Kybernetika-SPSE/RP-Hovorka/rp_dokumentace/LateX zdrojový kód/pictures/IMG_0316.JPG

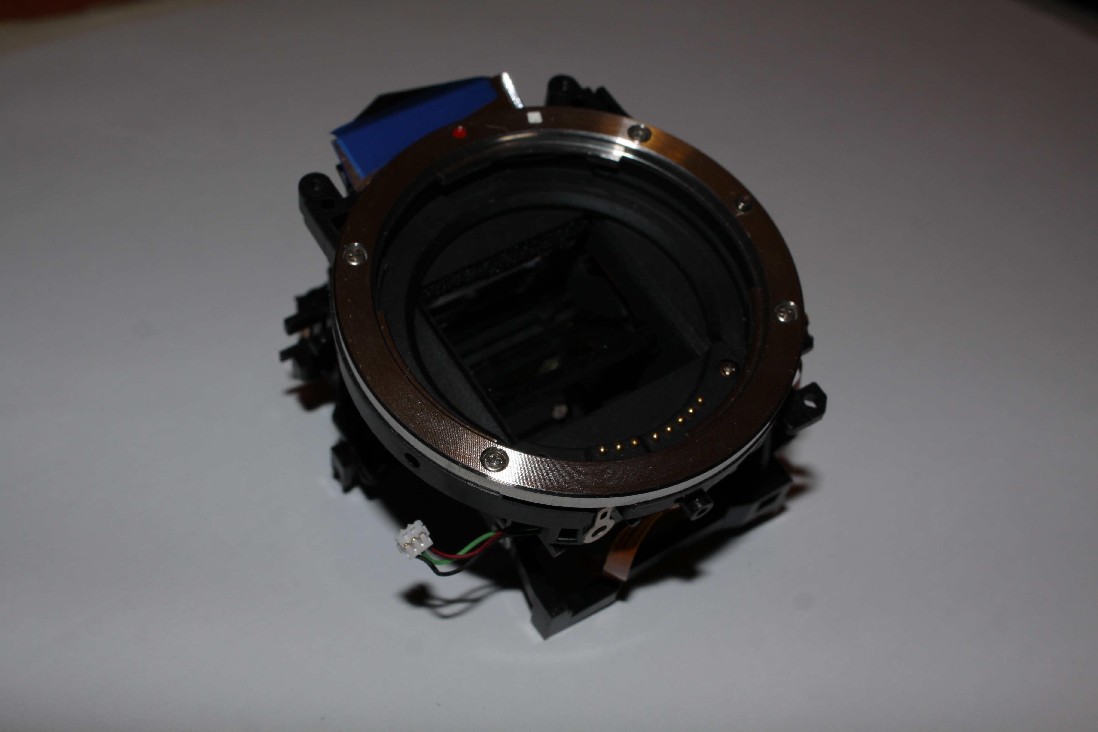
rp_dokumentace/LateX zdrojový kód/pictures/IMG_0316.JPG
